neoautus/Adelino/Adelino_X1.jpg

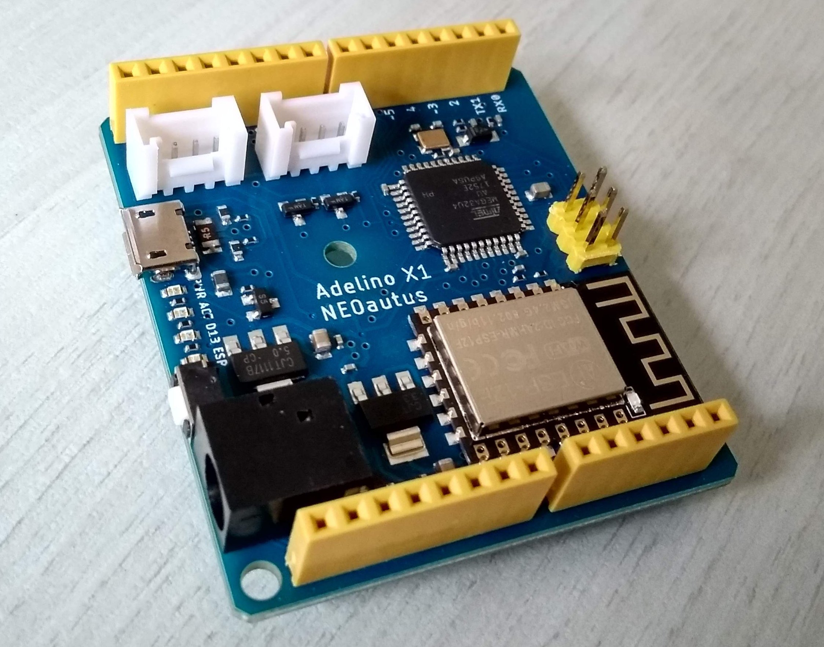
Adelino_X1.jpg
