neoautus/Adelino/Adelino_X2_PCB.jpg

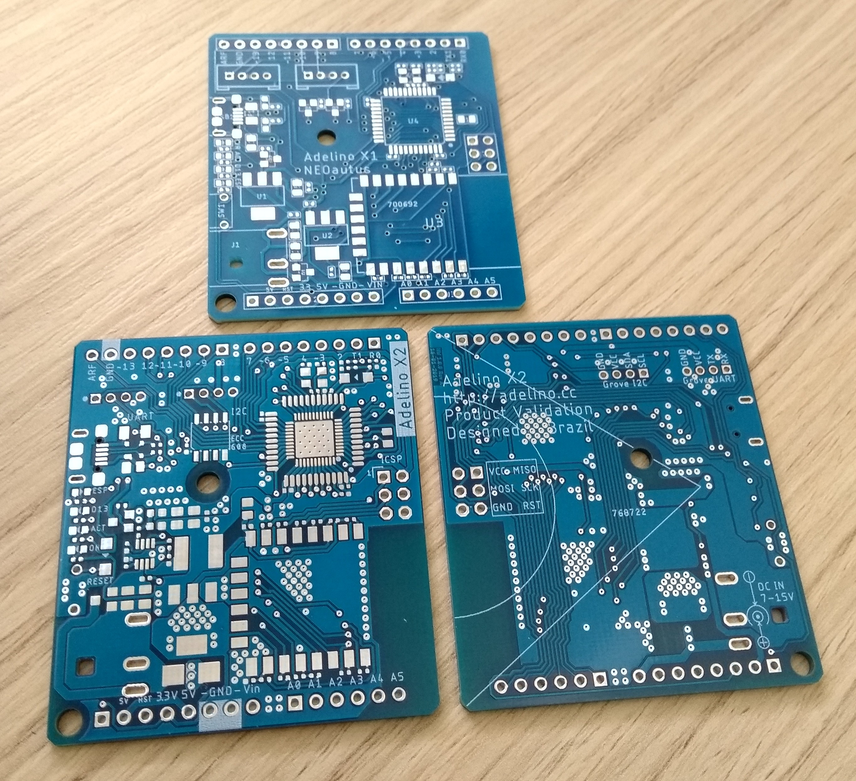
Adelino_X2_PCB.jpg
