neoautus/Adelino/Docs/adelino_its_alive.gif

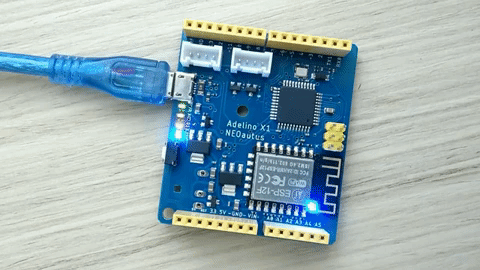
Docs/adelino_its_alive.gif
