neoautus/Adelino/Docs/Proporcoes_Bandeira_do_Brasil.png

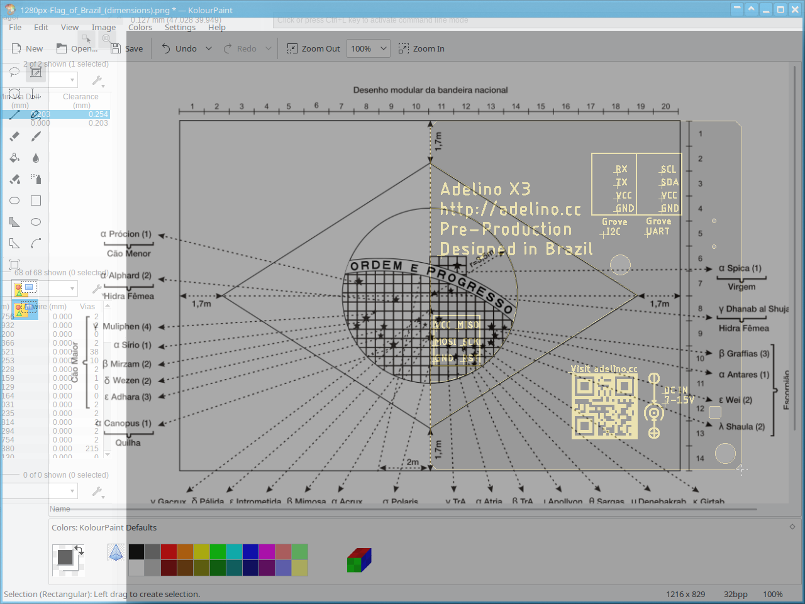
Docs/Proporcoes_Bandeira_do_Brasil.png
