neoautus/Adelino/Eagle/AdelinoR1_sch.png

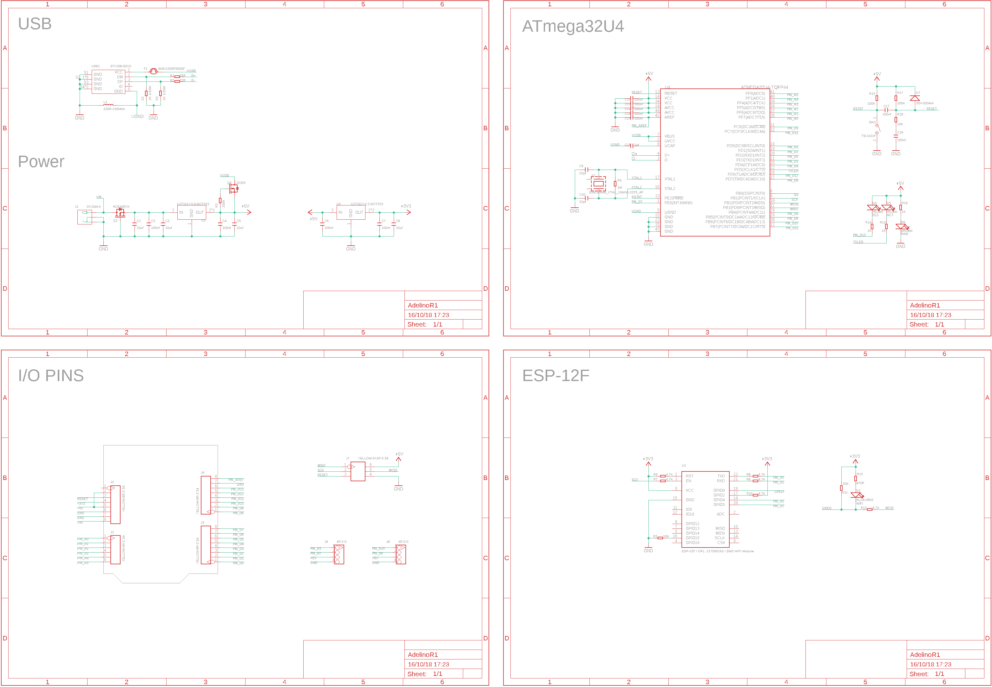
Eagle/AdelinoR1_sch.png
