neoautus/Adelino/Eagle/AdelinoR2_sch.png

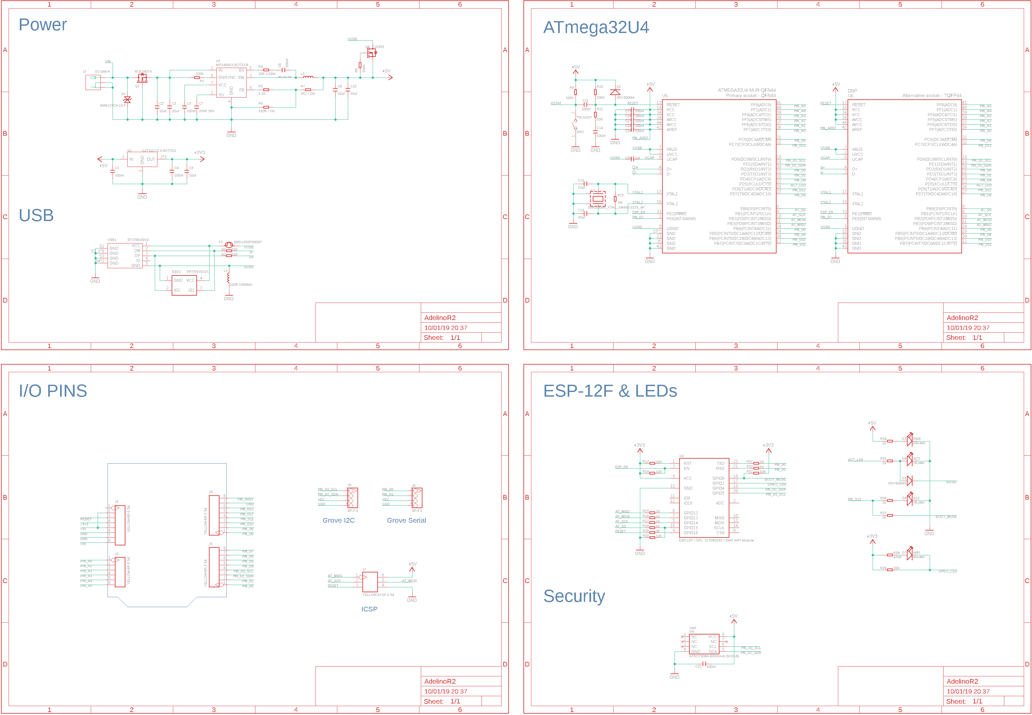
Eagle/AdelinoR2_sch.png
