neoautus/Adelino/Eagle/Project/AdelinoX2/AdelinoX2_brd.png

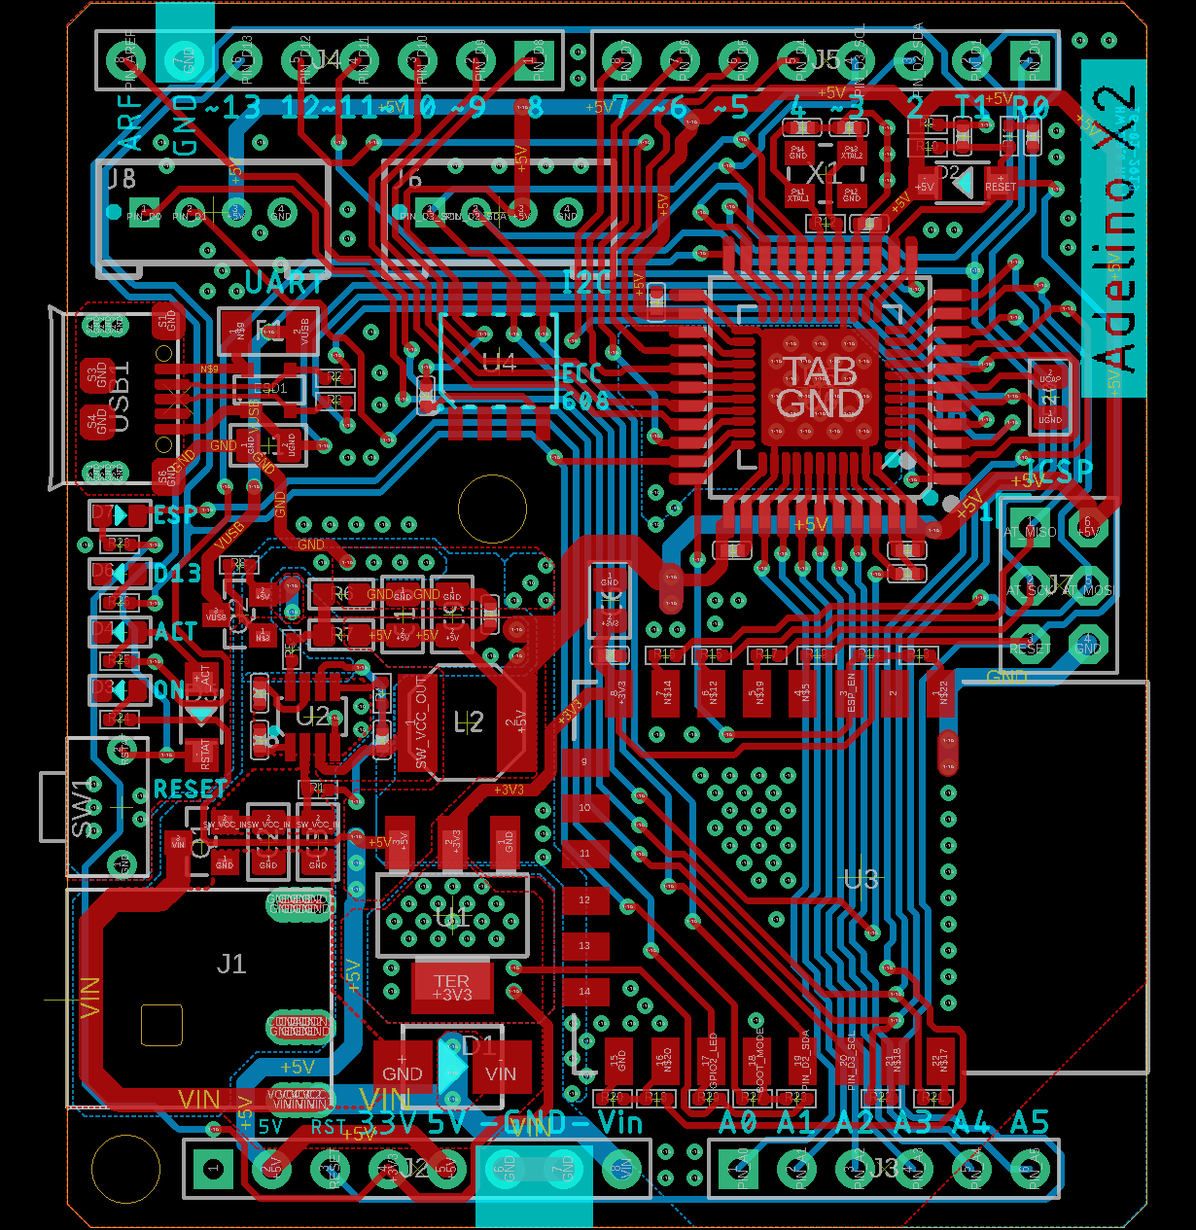
Eagle/Project/AdelinoX2/AdelinoX2_brd.png
