neoautus/Adelino/Pics/Adelino_Detalhe.jpg

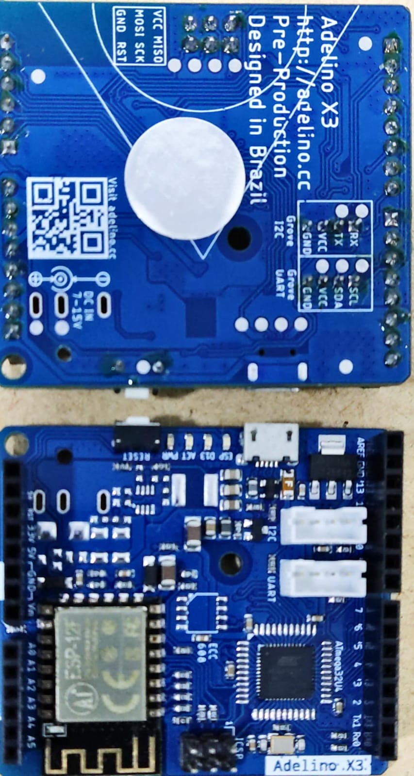
Pics/Adelino_Detalhe.jpg
