neoautus/Adelino/Pics/Adelino_validado_PTI (1).jpeg

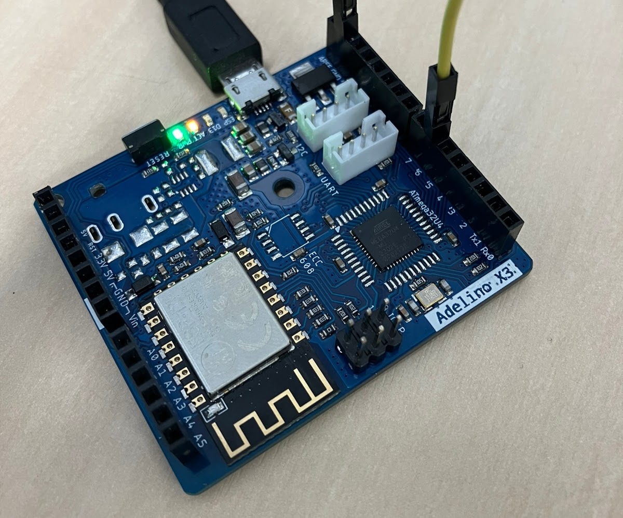
Pics/Adelino_validado_PTI (1).jpeg
