neoautus/Adelino/Pics/Adelino_validado_PTI.jpeg

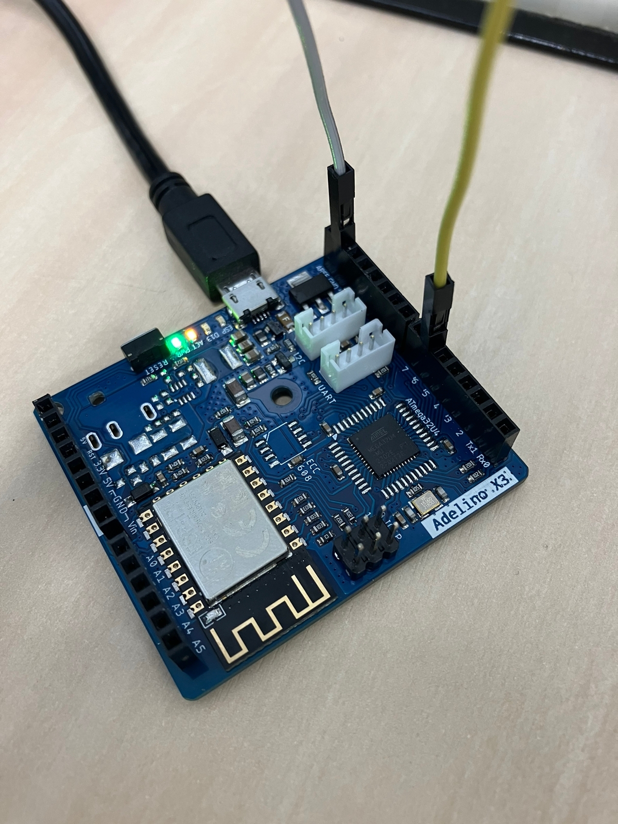
Pics/Adelino_validado_PTI.jpeg
