neoautus/Adelino/Pics/Adelino_X3_SeeedStudio.jpg

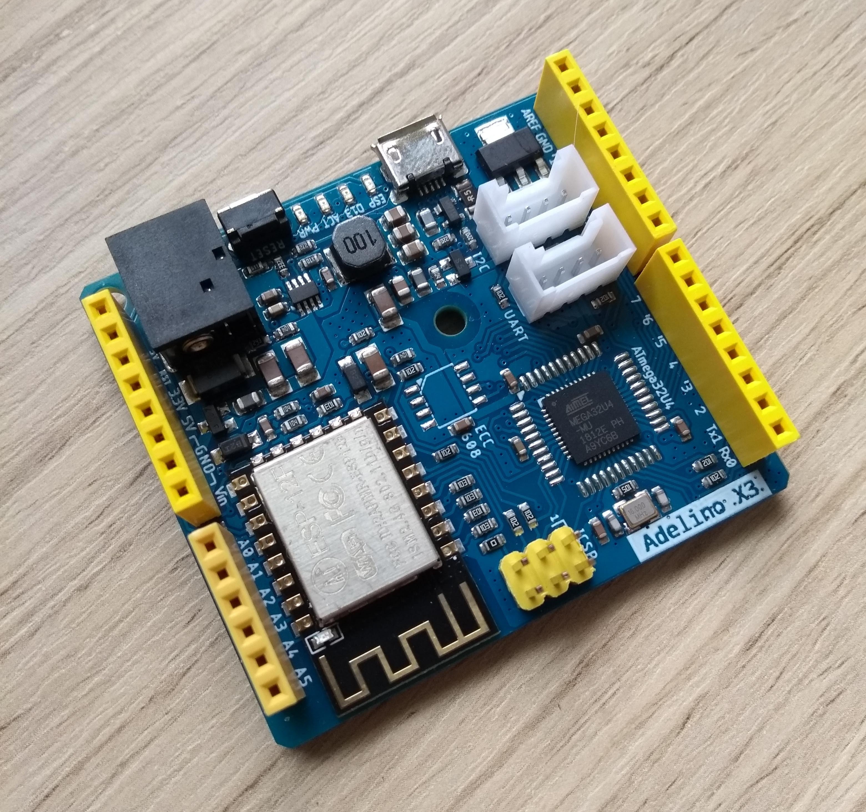
Pics/Adelino_X3_SeeedStudio.jpg
