neoautus/Adelino/Pics/Adelinos_festando (1).jpeg

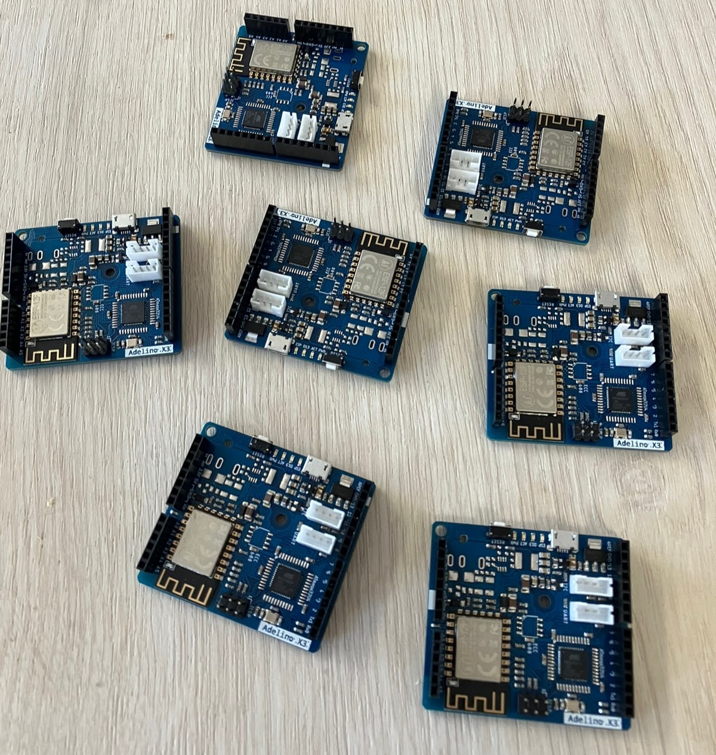
Pics/Adelinos_festando (1).jpeg
