neoautus/Adelino/Pics/Caixa_Adelinos_1.jpg

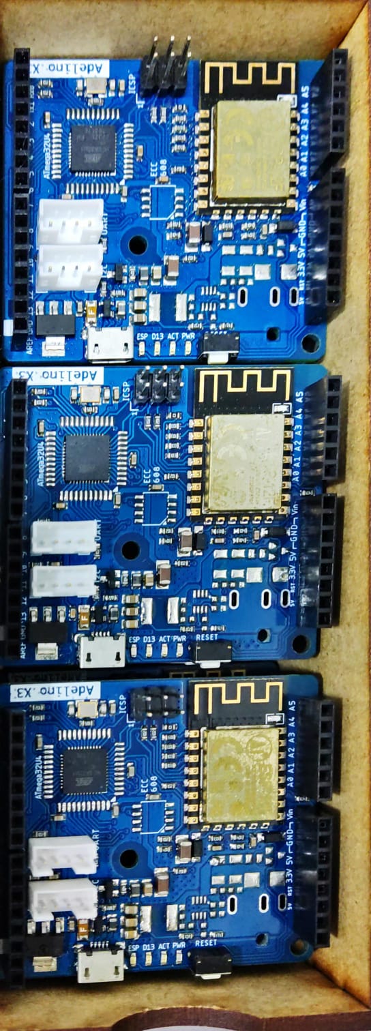
Pics/Caixa_Adelinos_1.jpg
