neoautus/Adelino/Pics/Caixa_Adelinos_2.jpg

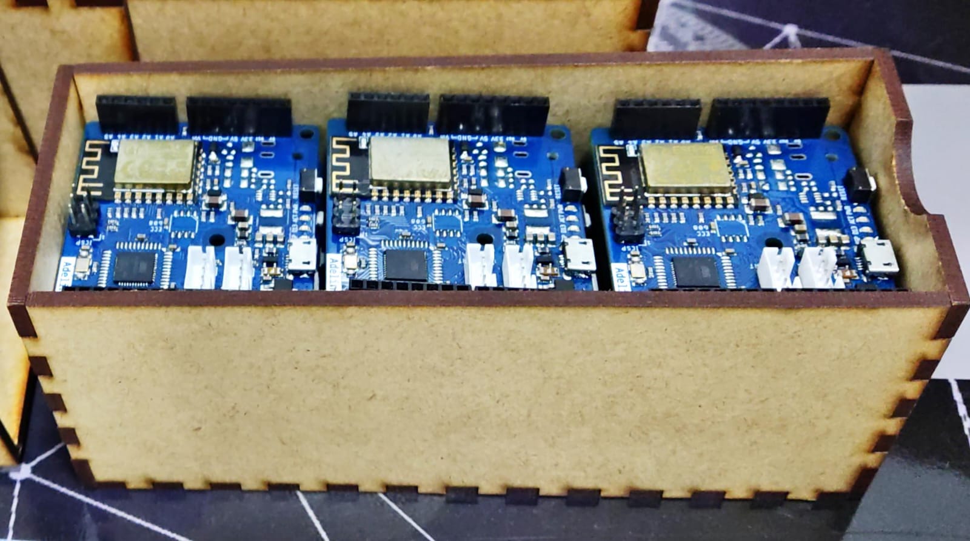
Pics/Caixa_Adelinos_2.jpg
