neoautus/Adelino/Pics/Caixa_Adelinos_3.jpeg

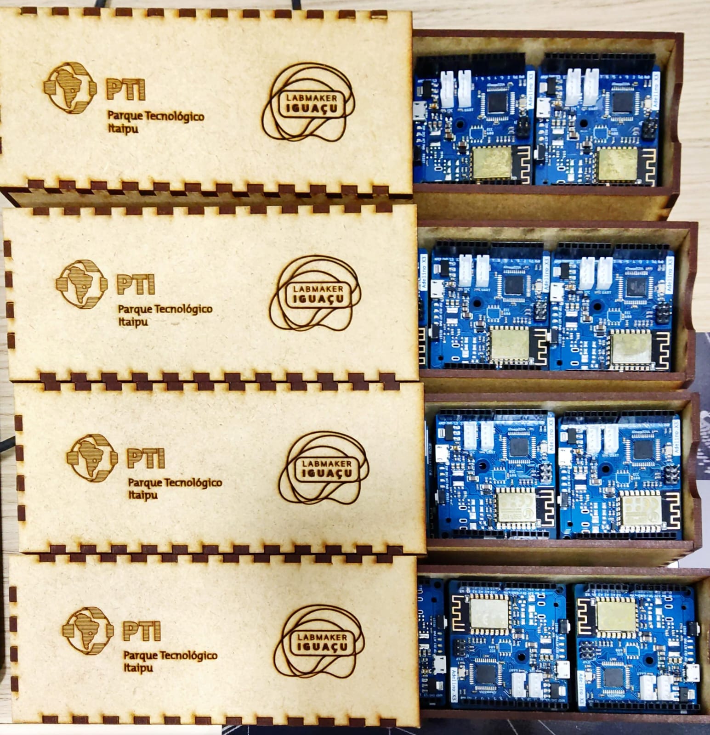
Pics/Caixa_Adelinos_3.jpeg
