neoautus/Adelino/Pics/Patches_adelino_X1.jpg

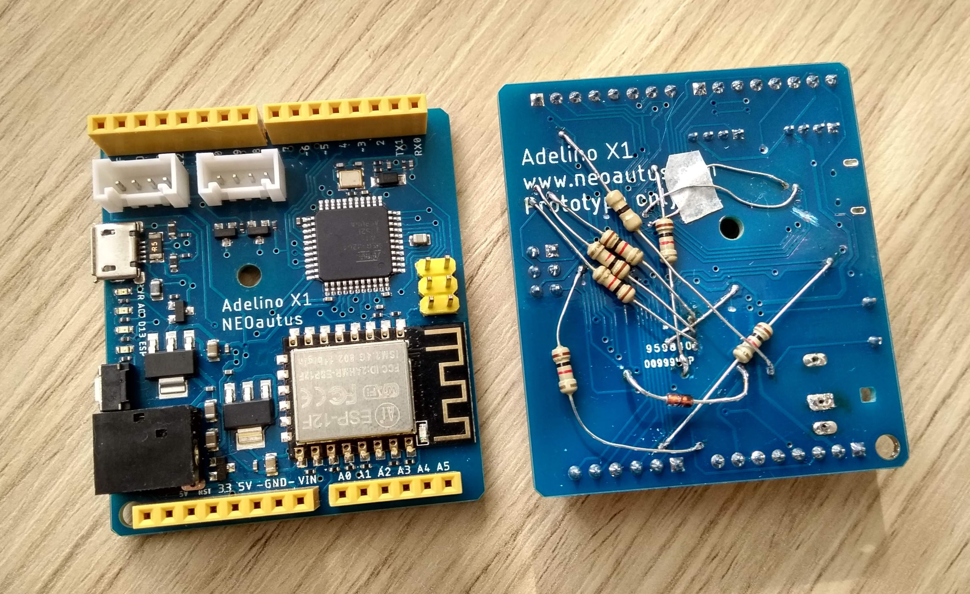
Pics/Patches_adelino_X1.jpg
