neoautus/Adelino/Pics/Redfi_instalado.jpg

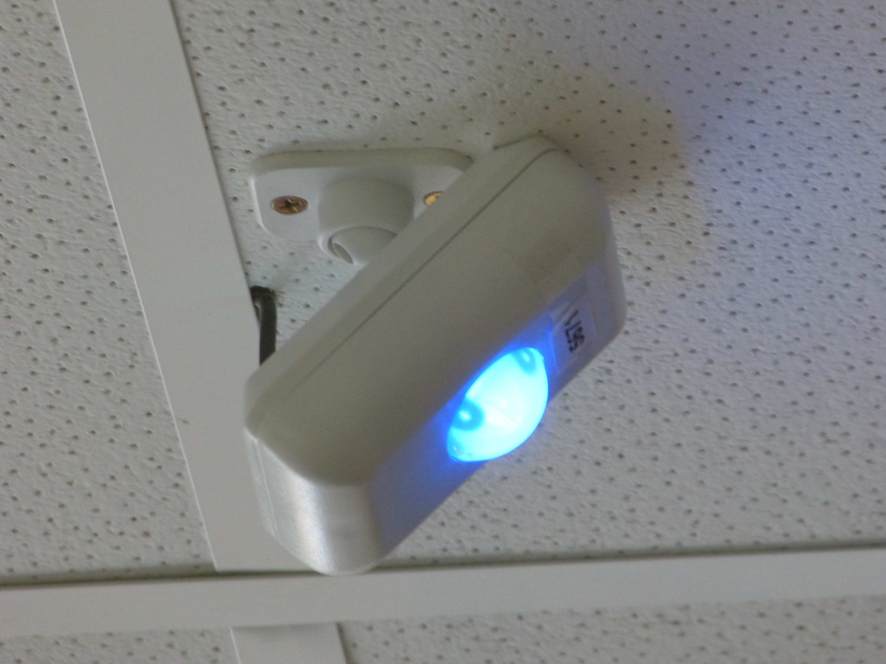
Pics/Redfi_instalado.jpg
