neoautus/Adelino/Pics/Redfi_Instalado_salao.jpg

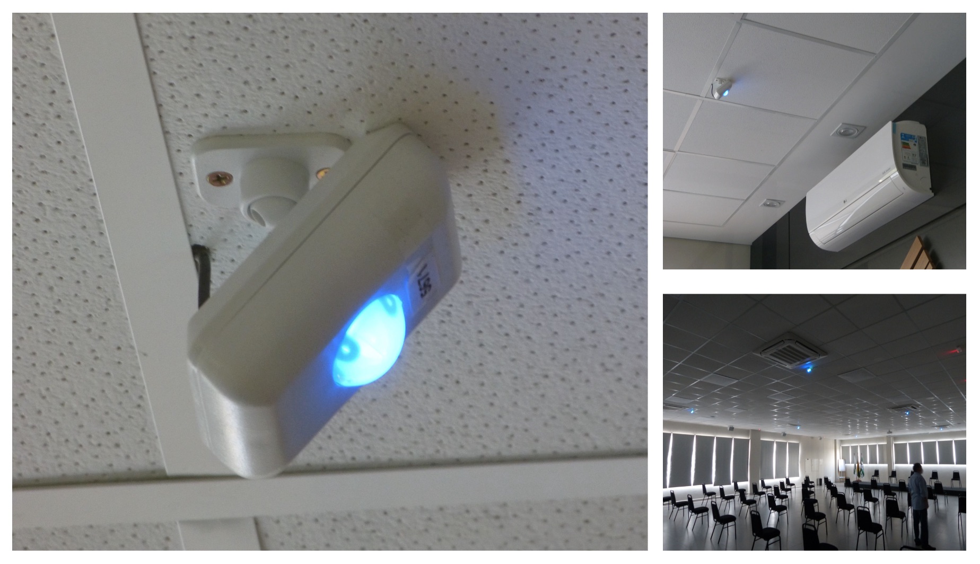
Pics/Redfi_Instalado_salao.jpg
