neoautus/Adelino/Pics/Redfi_produto.png

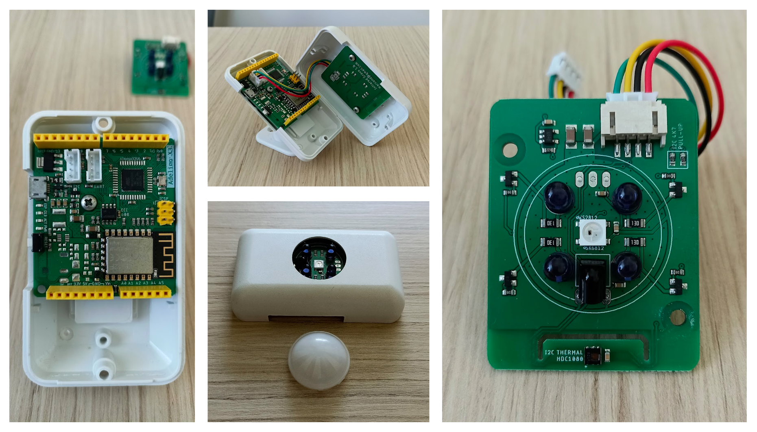
Pics/Redfi_produto.png
