neoautus/Adelino/Pics/Reset_pulso.png

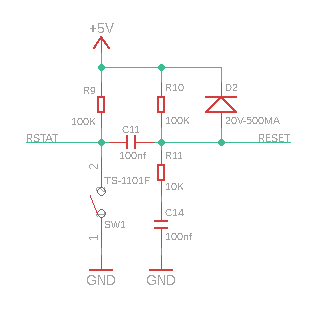
Pics/Reset_pulso.png
