neoautus/Adelino/Pics/Video Centelha.jpg

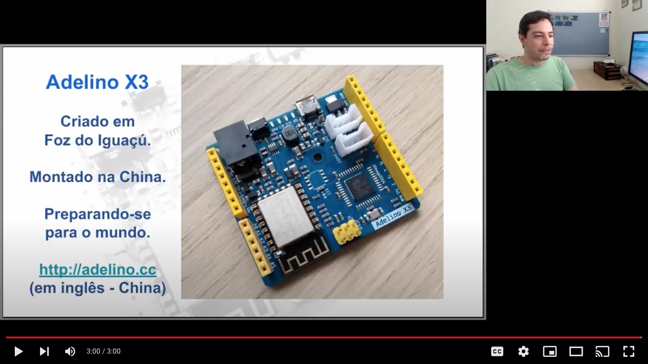
Pics/Video Centelha.jpg
