neoautus/Adelino/POHW.png

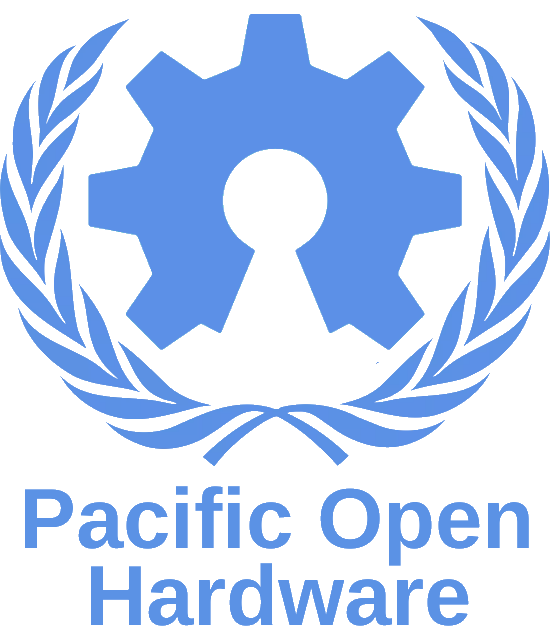
POHW.png
